ULAS-HiPR/croi/firmware/src/platform/stm_f0.h

#ifdef F0
#ifndef STM_F072xB_H
#define STM_F072xB_H

#include "stm32f0xx_hal.h"
#include "stm32f0xx_hal_spi.h"
#include "stm32f0xx_hal_gpio.h"
#include "error_handler.h"

#define BUZZER_GPIO_PORT GPIOB
#define BUZZER_GPIO_PIN GPIO_PIN_0
#define BUZZER_TIMER_TICK_HZ 1000000U

#define SPI_SCK_PIN GPIO_PIN_5 
#define SPI_MISO_PIN GPIO_PIN_6 
#define SPI_MOSI_PIN GPIO_PIN_7 
#define SPI_GPIO_PORT GPIOA 
#define SPI_GPIO_CLK_ENABLE() __HAL_RCC_GPIOA_CLK_ENABLE() 

#define IMU_CS_PIN GPIO_PIN_11
#define IMU_CS_PORT GPIOB

#define FLASH_CS_PIN GPIO_PIN_12
#define FLASH_CS_PORT GPIOB
#define FLASH_CS_GPIO_CLK_ENABLE() __HAL_RCC_GPIOB_CLK_ENABLE()

#define BME680_CS_PIN GPIO_PIN_14
#define BME680_CS_PORT GPIOB

#define ADXL375_CS_PIN GPIO_PIN_15
#define ADXL375_CS_PORT GPIOB

#define BARO_CS_PIN GPIO_PIN_4
#define BARO_CS_PORT GPIOB

extern SPI_HandleTypeDef hspi1;
extern CAN_HandleTypeDef hcan;
extern TIM_HandleTypeDef htim3;

// Initialization functions
void MX_SPI1_Init();
void MX_CAN_Init();
void MX_GPIO_Init();
void MX_TIM3_Init(void);

#endif // STM_F4_H
#endif // F4
